Rhetticle/The-Big-One/TBO CAD/STL Files/Barrel/Barrel Top/Barrel top long.stl

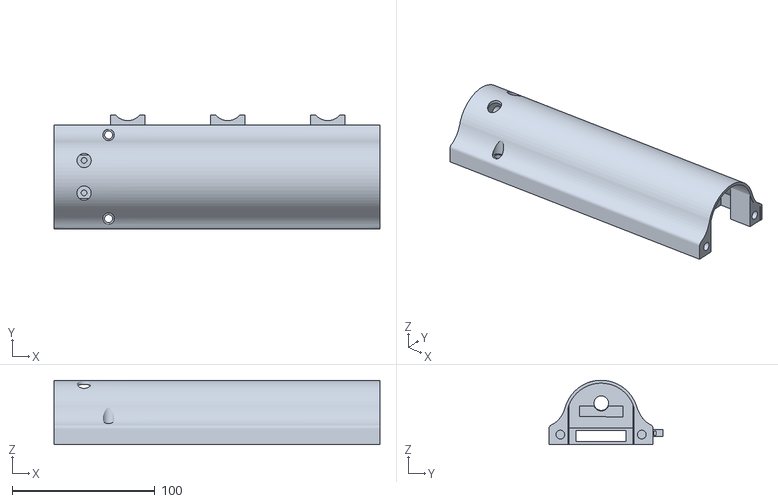
[picture p15: CAD file, 2024-03-29]
TBO CAD/STL Files/Barrel/Barrel Top/Barrel top long.stl
228.1 x 79.9 x 45.0
