Rhetticle/The-Big-One/TBO CAD/STL Files/Coil Stop.stl

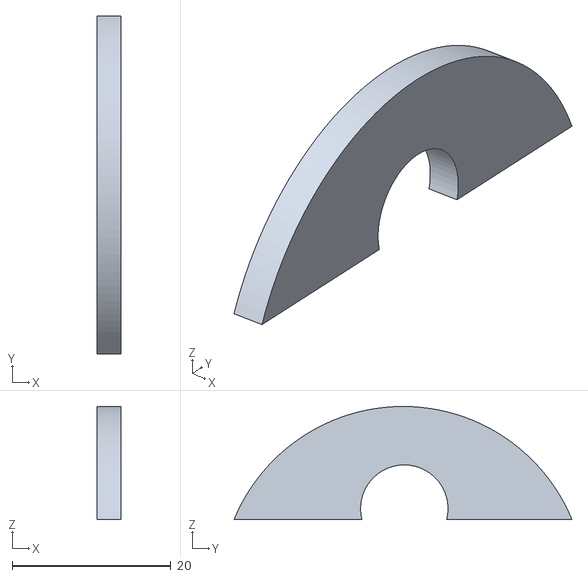
[picture p16: CAD file, 2024-03-29]
TBO CAD/STL Files/Coil Stop.stl
3.00 x 42.5 x 14.2
