Rhetticle/The-Big-One/TBO CAD/STL Files/Handle/Handle.stl

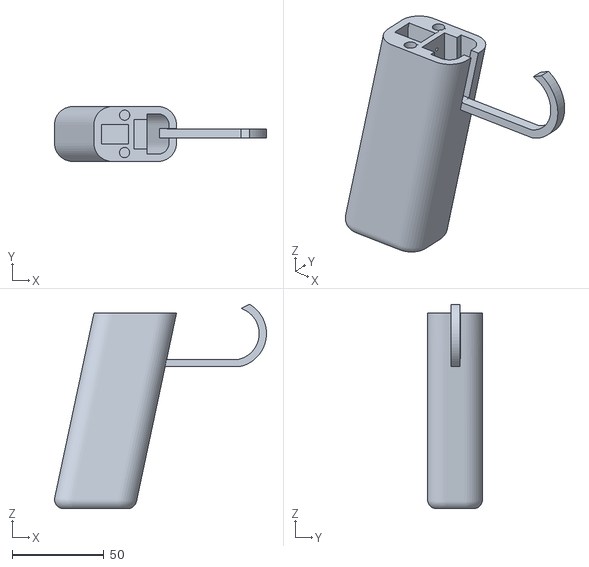
[picture p17: CAD file, 2024-03-29]
TBO CAD/STL Files/Handle/Handle.stl
115.5 x 30.0 x 111.3
