Rhetticle/The-Big-One/TBO CAD/STL Files/Middle/Middle plate.stl

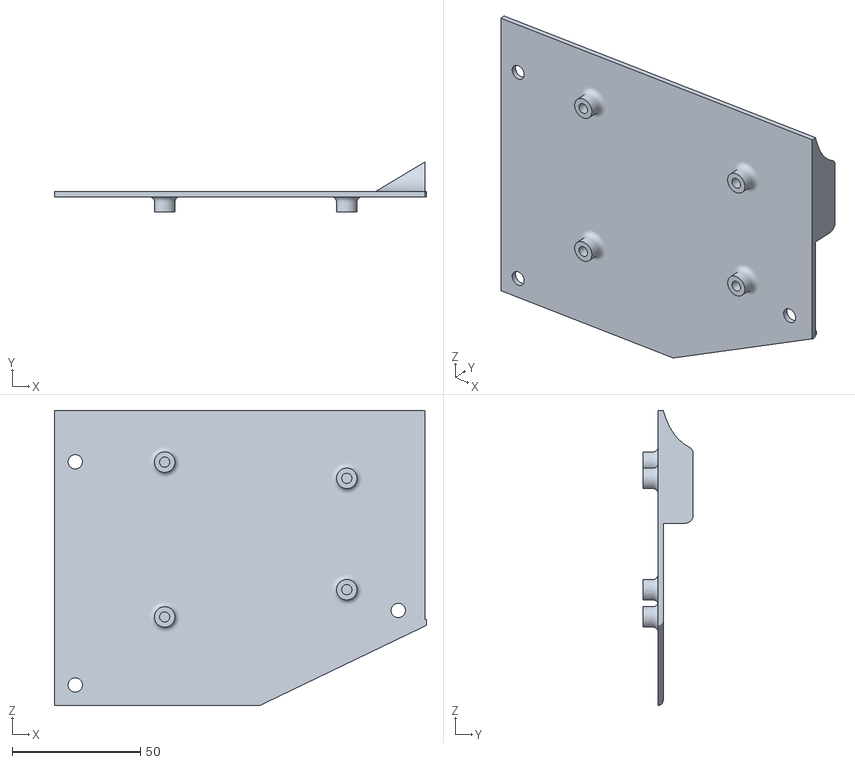
[picture p18: CAD file, 2024-03-29]
TBO CAD/STL Files/Middle/Middle plate.stl
145.0 x 19.7 x 115.0
