Rhetticle/The-Big-One/TBO CAD/STL Files/Stock/Battery clip.stl

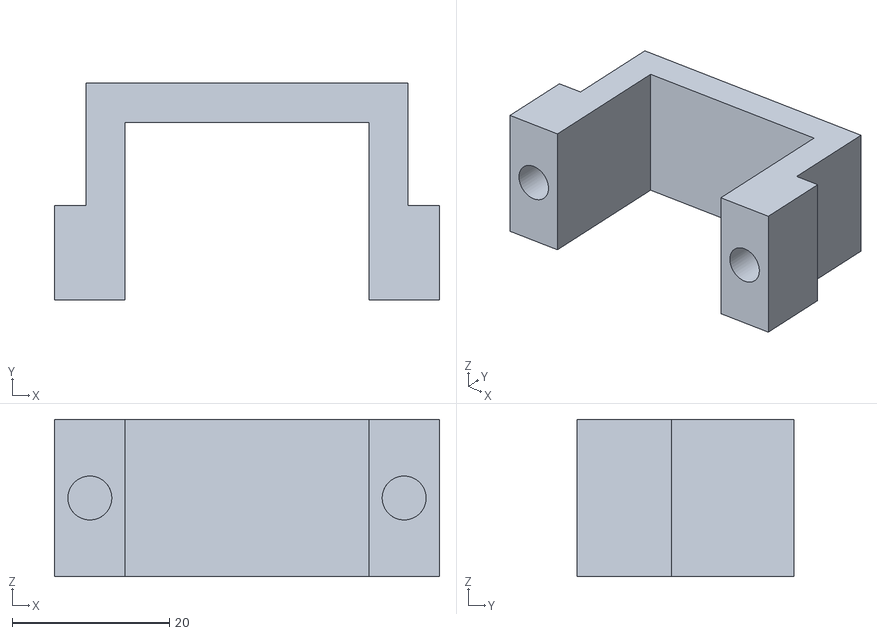
[picture p19: CAD file, 2024-03-29]
TBO CAD/STL Files/Stock/Battery clip.stl
49.0 x 27.6 x 20.0
