Rhetticle/The-Big-One/TBO CAD/STL Files/Barrel/Barrel Top/laser clamp.stl

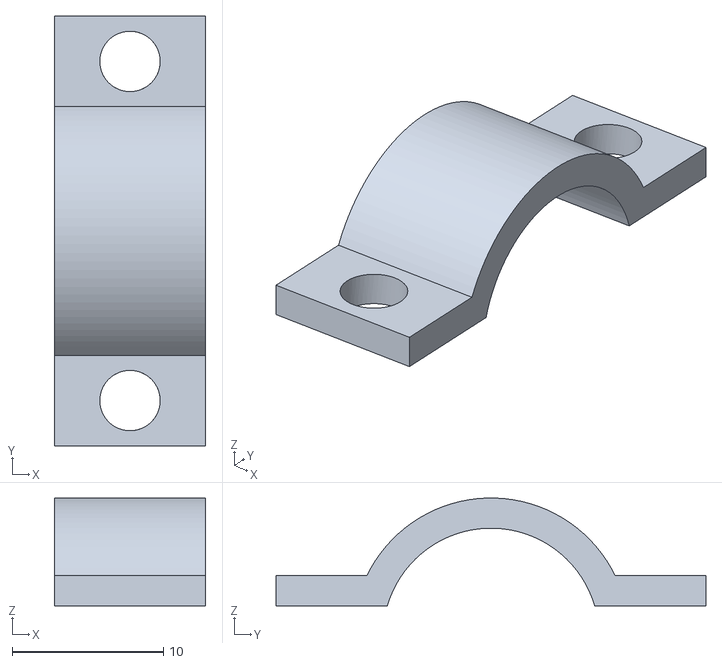
[picture p20: CAD file, 2024-03-29]
TBO CAD/STL Files/Barrel/Barrel Top/laser clamp.stl
10.0 x 28.5 x 7.15
