Rhetticle/The-Big-One/TBO CAD/STL Files/Foregrip.stl

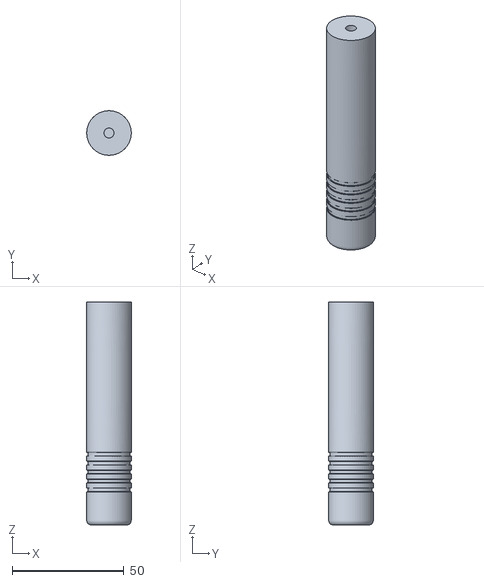
[picture p21: CAD file, 2024-03-29]
TBO CAD/STL Files/Foregrip.stl
20.0 x 20.0 x 100.0
