Rhetticle/The-Big-One/TBO CAD/STL Files/Middle/New Middle.stl

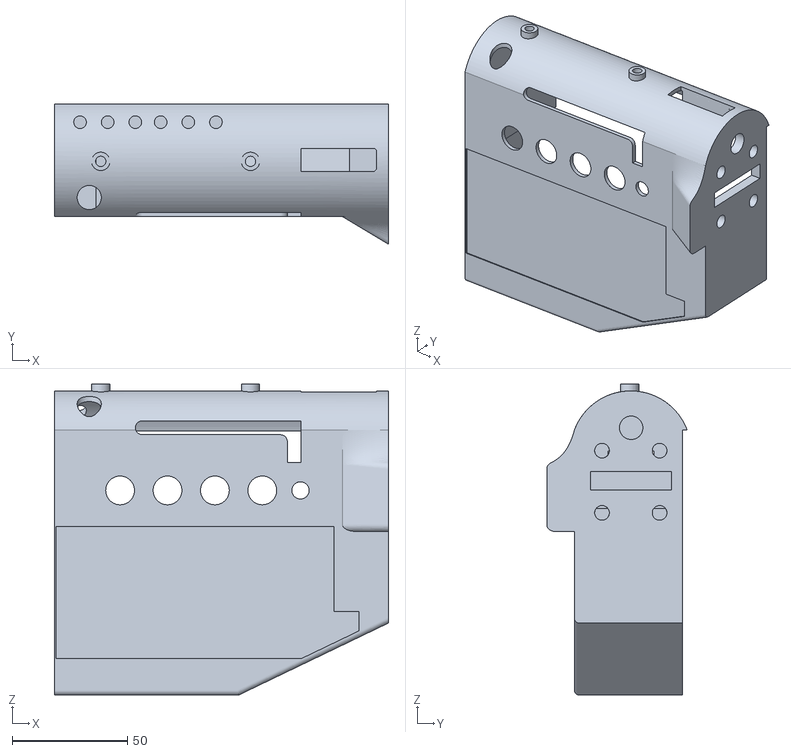
[picture p22: CAD file, 2024-03-29]
TBO CAD/STL Files/Middle/New Middle.stl
145.0 x 61.0 x 135.0
