Rhetticle/The-Big-One/TBO CAD/STL Files/Stock/transformer compartment lid.stl

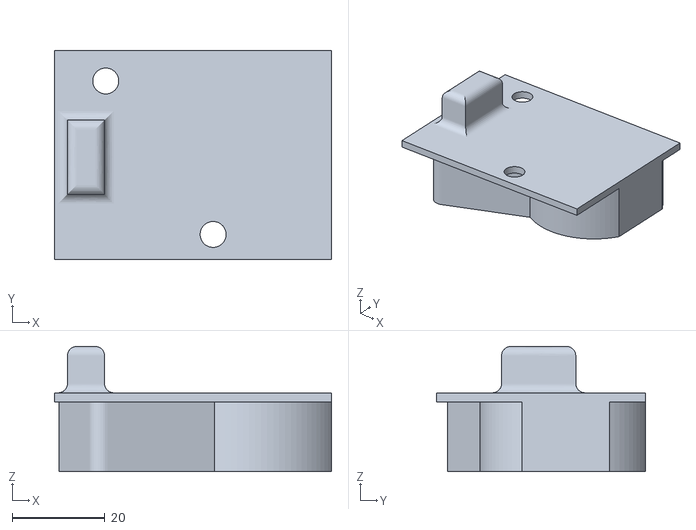
[picture p23: CAD file, 2024-03-29]
TBO CAD/STL Files/Stock/transformer compartment lid.stl
59.7 x 45.0 x 27.0
