Rhetticle/The-Big-One/TBO CAD/STL Files/Middle/Middle Section Spacer.stl

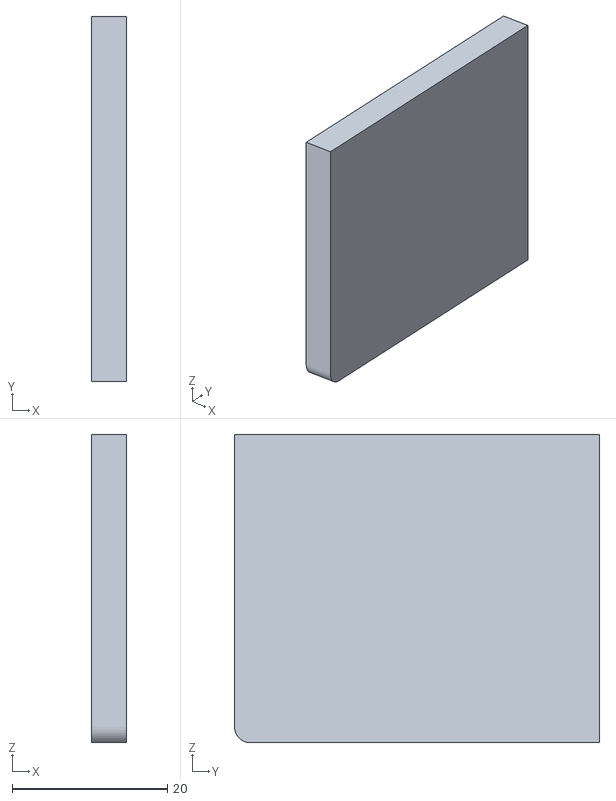
[picture p24: CAD file, 2024-03-29]
TBO CAD/STL Files/Middle/Middle Section Spacer.stl
4.50 x 47.0 x 39.7
