Rhetticle/The-Big-One/TBO CAD/STL Files/Stock/New Stock.stl

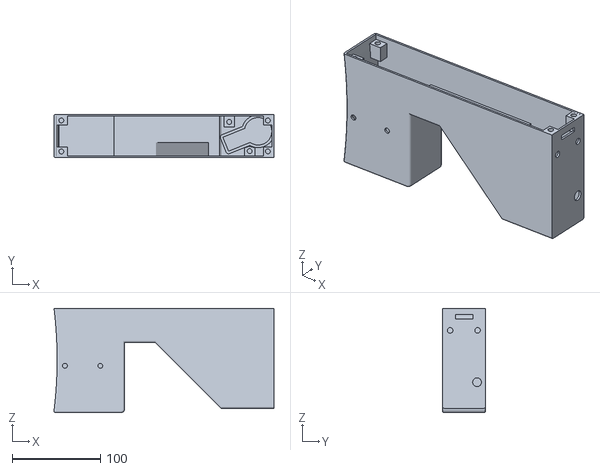
[picture p25: CAD file, 2024-03-29]
TBO CAD/STL Files/Stock/New Stock.stl
248.7 x 49.0 x 118.0
