Rhetticle/The-Big-One/TBO CAD/STL Files/Middle/Logo.stl

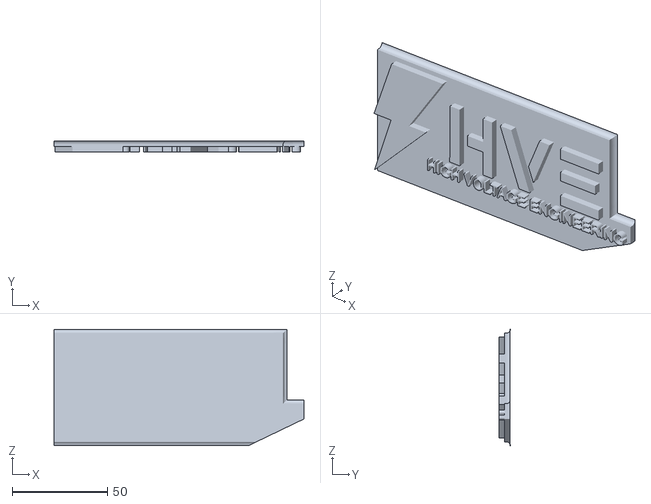
[picture p26: CAD file, 2024-03-29]
TBO CAD/STL Files/Middle/Logo.stl
131.2 x 6.00 x 61.0
